ViviLazuli/mtf-capacitive/docs/reverse-engineering/raw/dE0Tj.jpg

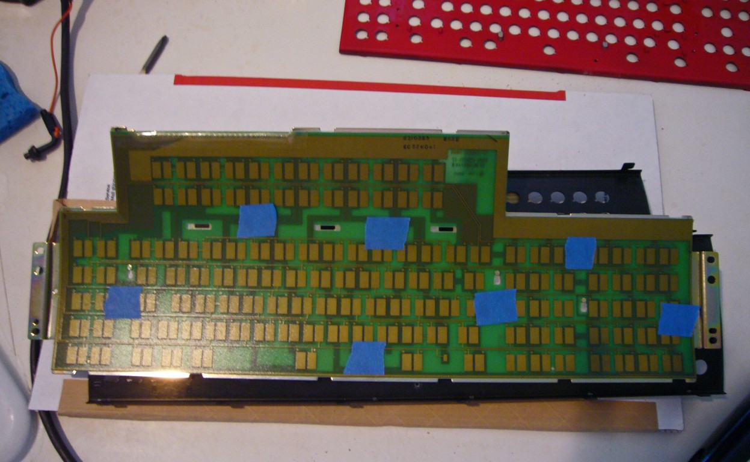
docs/reverse-engineering/raw/dE0Tj.jpg
