ViviLazuli/mtf-capacitive/docs/reverse-engineering/raw/7DLCNan.jpg

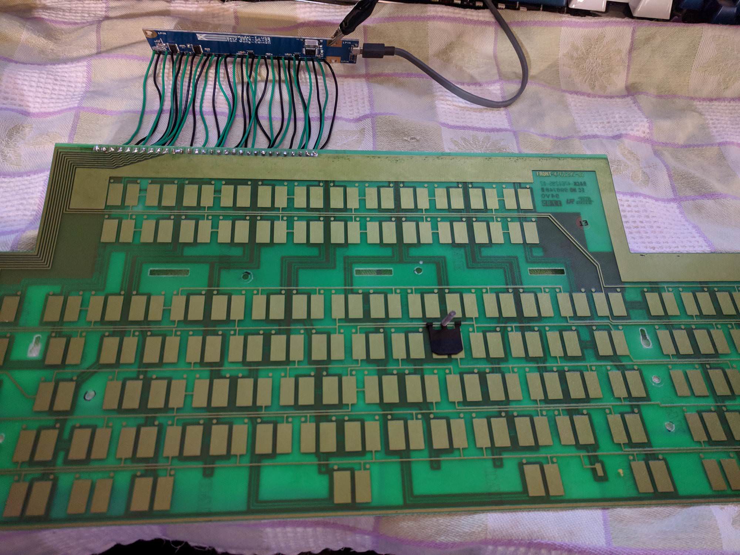
docs/reverse-engineering/raw/7DLCNan.jpg
