ViviLazuli/mtf-capacitive/docs/reverse-engineering/1.png

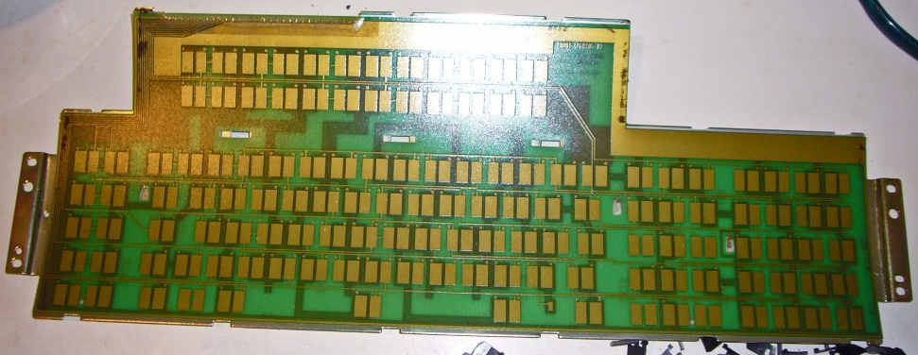
docs/reverse-engineering/1.png
