ViviLazuli/mtf-capacitive/docs/reverse-engineering/3.png

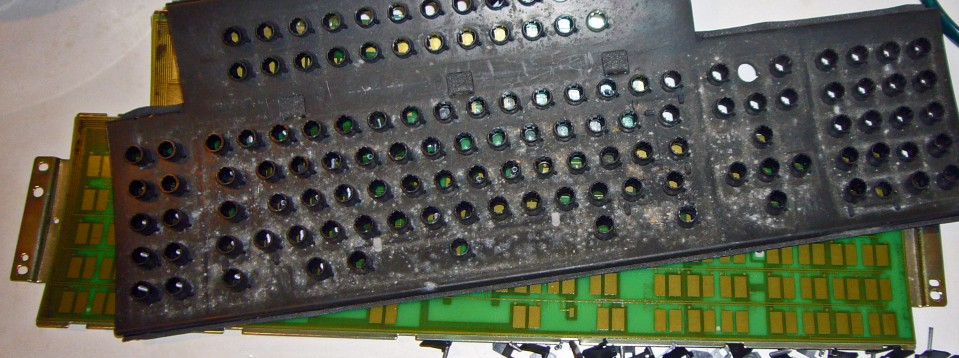
docs/reverse-engineering/3.png
