ViviLazuli/mtf-capacitive/docs/reverse-engineering/4.png

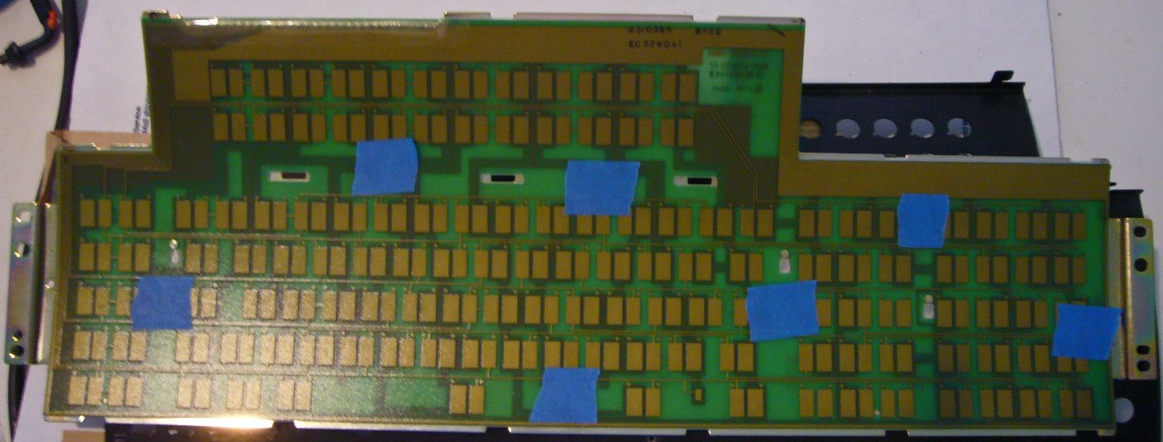
docs/reverse-engineering/4.png
