ViviLazuli/mtf-capacitive/docs/reverse-engineering/5.png

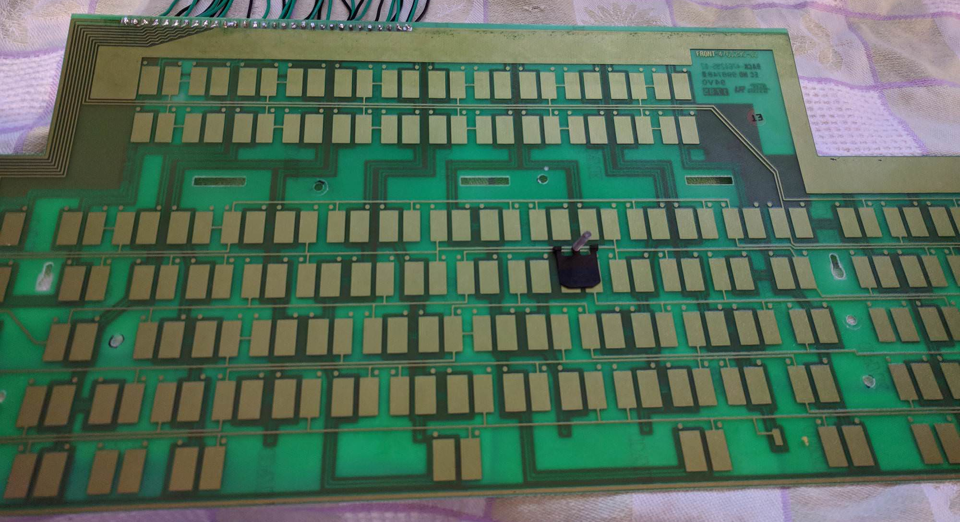
docs/reverse-engineering/5.png
