ViviLazuli/mtf-capacitive/docs/reverse-engineering/raw/5ufWd.jpg

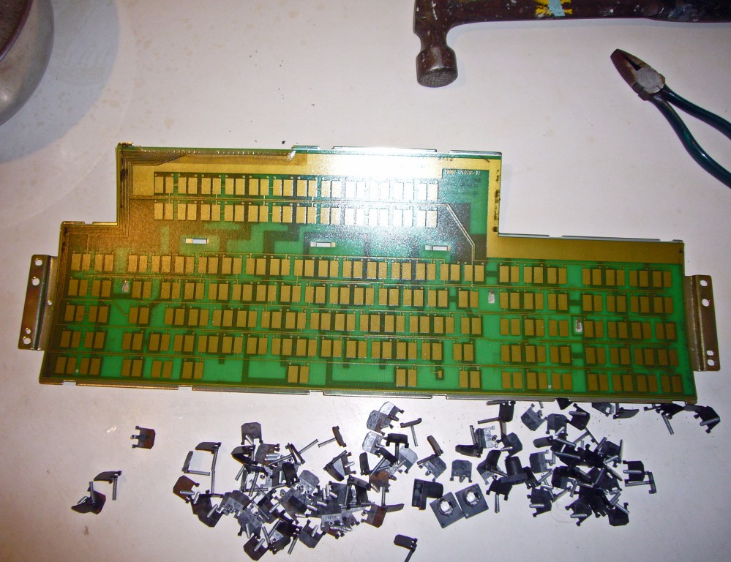
docs/reverse-engineering/raw/5ufWd.jpg
