ViviLazuli/mtf-capacitive/docs/reverse-engineering/raw/6Nk7qeI.jpg

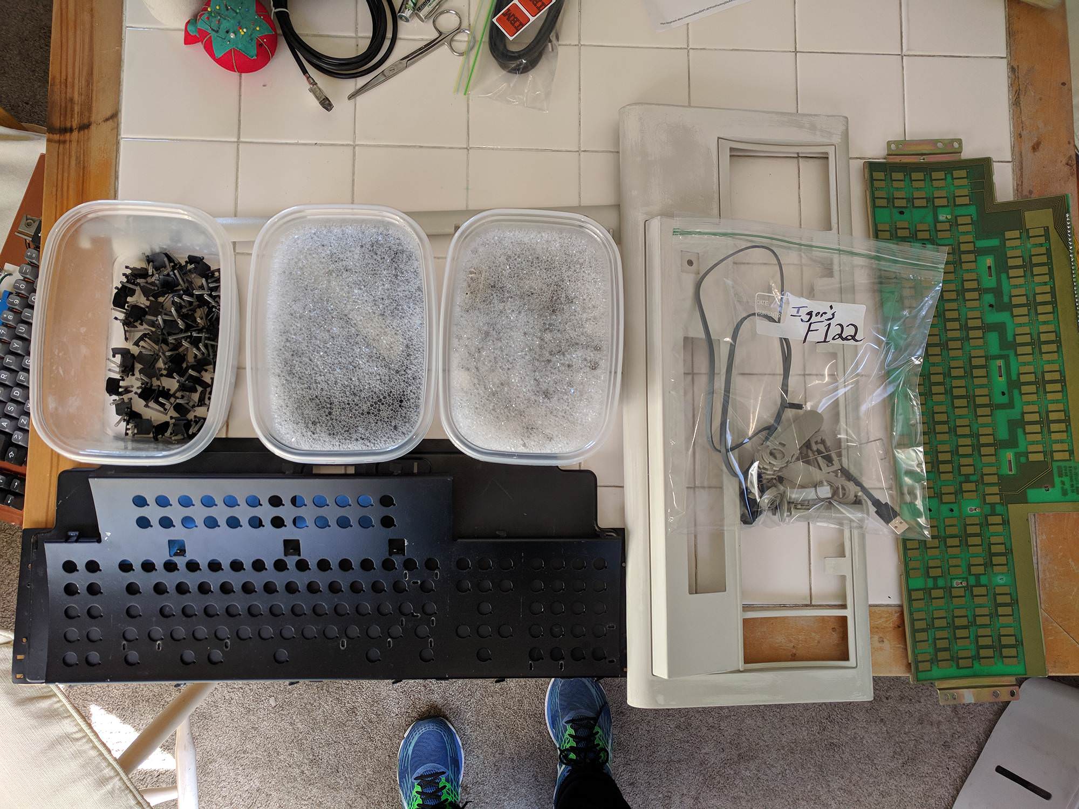
docs/reverse-engineering/raw/6Nk7qeI.jpg
