ViviLazuli/mtf-capacitive/docs/reverse-engineering/raw/hRpmc.jpg

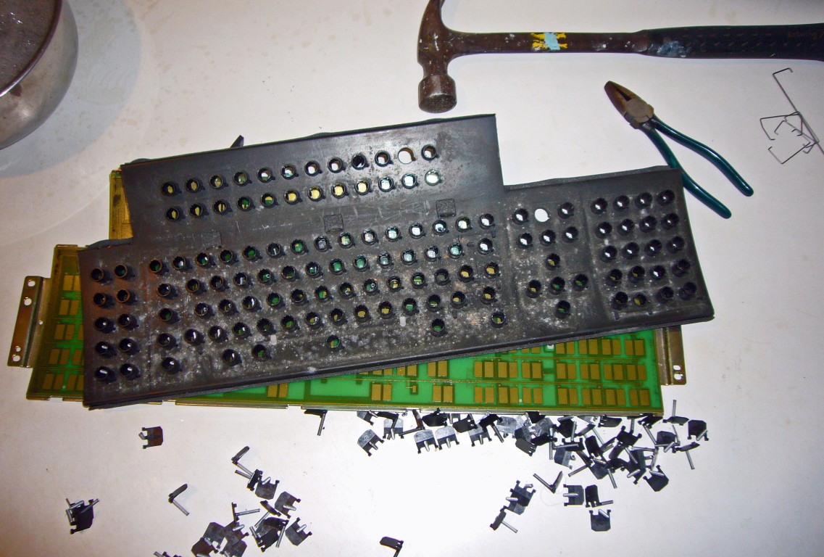
docs/reverse-engineering/raw/hRpmc.jpg
